Shijia0366/Environmental_Sensor_Group6/Environmental_Sensor_Group6/Enclosure/Right-Angle Female connector.SLDPRT

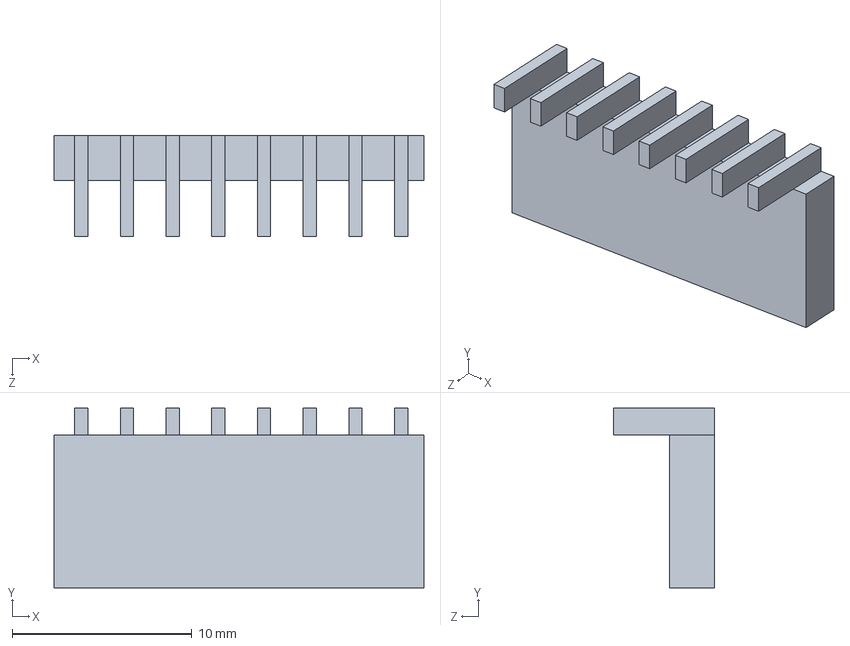
[picture p11: CAD file, 2025-12-15]
Environmental_Sensor_Group6/Enclosure/Right-Angle Female connector.SLDPRT
20.6 x 10.0 x 5.60 mm
