Shijia0366/Environmental_Sensor_Group6/Environmental_Sensor_Group6/Enclosure/button fitting component.SLDPRT

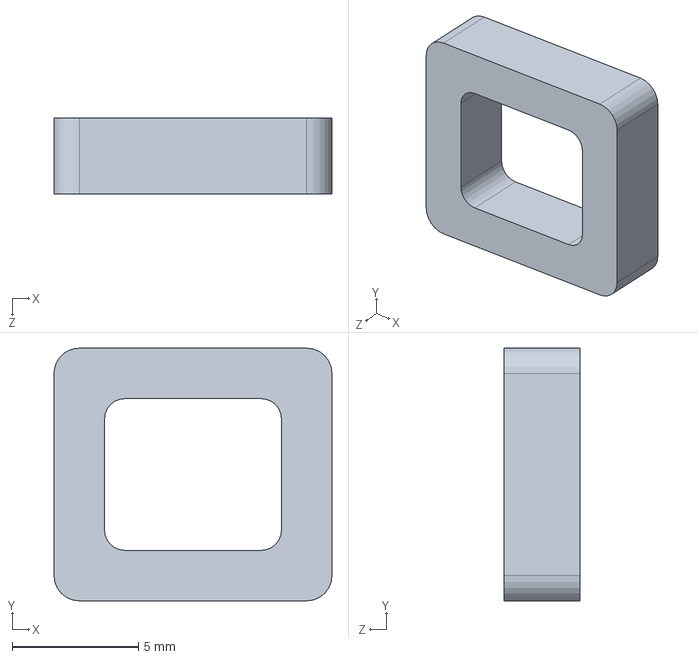
[picture p12: CAD file, 2025-12-15]
Environmental_Sensor_Group6/Enclosure/button fitting component.SLDPRT
11.0 x 10.0 x 3.00 mm
