Shijia0366/Environmental_Sensor_Group6/Environmental_Sensor_Group6/Enclosure/environmental pcb.step

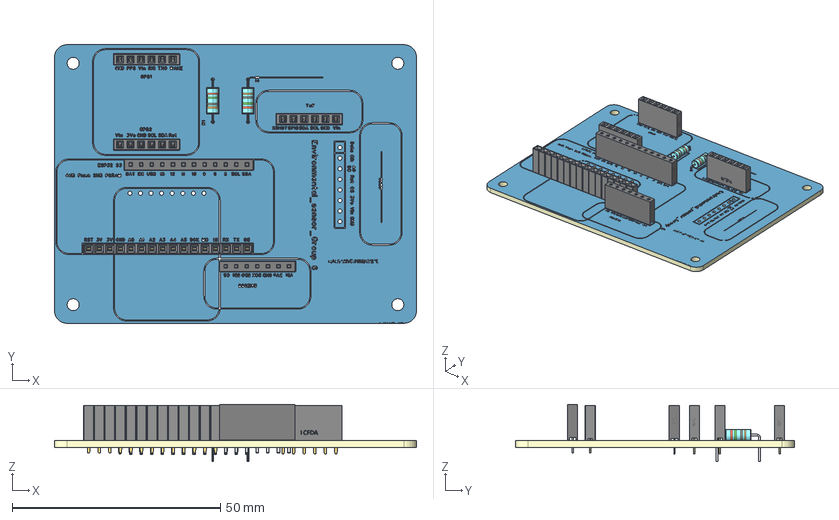
[picture p13: CAD file, 2025-12-15]
Environmental_Sensor_Group6/Enclosure/environmental pcb.step
87.0 x 67.0 x 13.7 mm
Board~KTJj
TopCopper~KTJj
BottomCopper~KTJj
TopSilkscreen~KTJj
BottomSilkscreen~KTJj
TopFpcStiffener~KTJj
BottomFpcStiffener~KTJj
HDR-TH_7P-P2.54-V-F~HDR-TH_7P-P2.54-F-LI-1X7P~KTJj
HDR-TH_12P-P2.54-V-F~HDR-TH_12P-P2.54-F-LI-1X12P~KTJj
HDR-TH_6P-P2.54-V-F~HDR-TH_6P-P2.54-V-F~KTJj x 3
HDR-TH_16P-P2.54-V-F-1~HDR2.54-F-LI-1X16P~KTJj
RES-TH_BD2.7-L6.2-P10.20-D0.4~RES-TH_BD2.7-L6.2-P10.20-D0.4~KTJj x 2
