Shijia0366/Environmental_Sensor_Group6/Environmental_Sensor_Group6/Enclosure/Button.SLDPRT

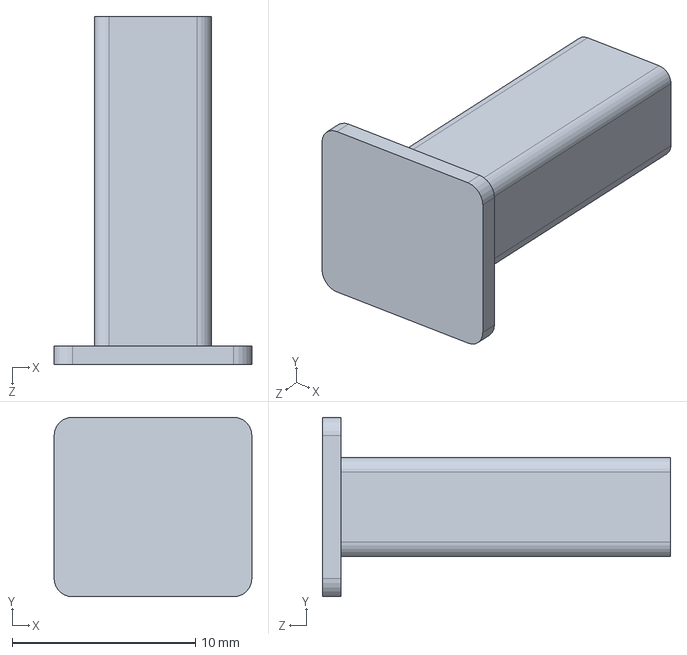
[picture p14: CAD file, 2025-12-15]
Environmental_Sensor_Group6/Enclosure/Button.SLDPRT
10.8 x 9.80 x 19.0 mm
