Shijia0366/Environmental_Sensor_Group6/Environmental_Sensor_Group6/Enclosure/oled.SLDPRT

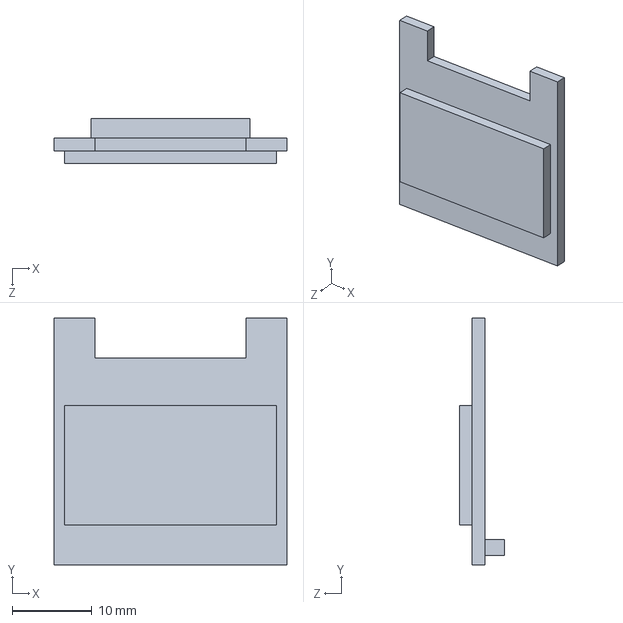
[picture p15: CAD file, 2025-12-15]
Environmental_Sensor_Group6/Enclosure/oled.SLDPRT
29.2 x 31.0 x 5.70 mm
