Shijia0366/Environmental_Sensor_Group6/Environmental_Sensor_Group6/Enclosure/Enclosure design 3D Group 6 - button-1.STL

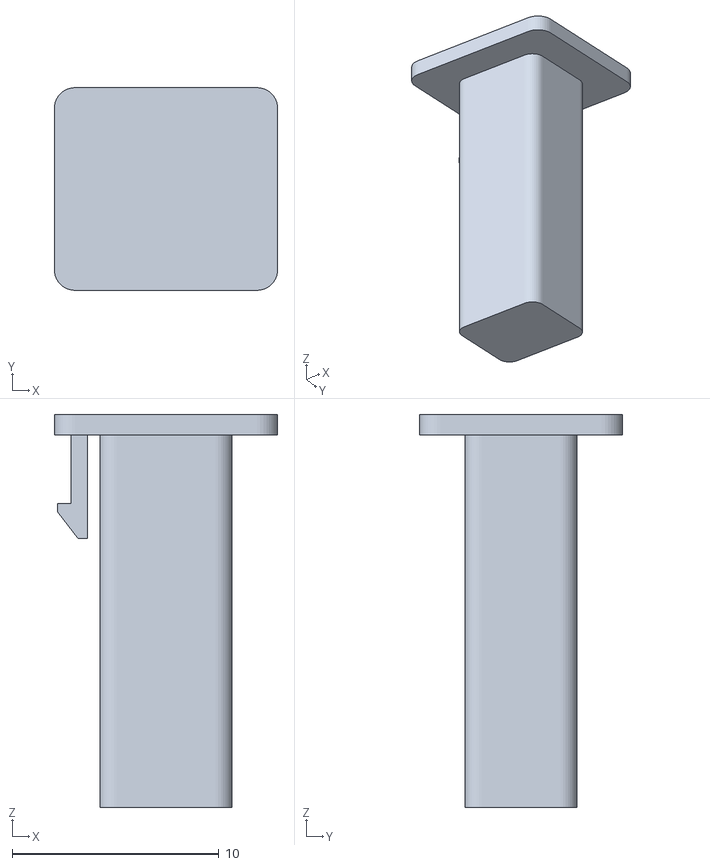
[picture p16: CAD file, 2025-12-15]
Environmental_Sensor_Group6/Enclosure/Enclosure design 3D Group 6 - button-1.STL
10.8 x 9.80 x 19.0
