Shijia0366/Environmental_Sensor_Group6/Environmental_Sensor_Group6/Enclosure/esp32.SLDPRT

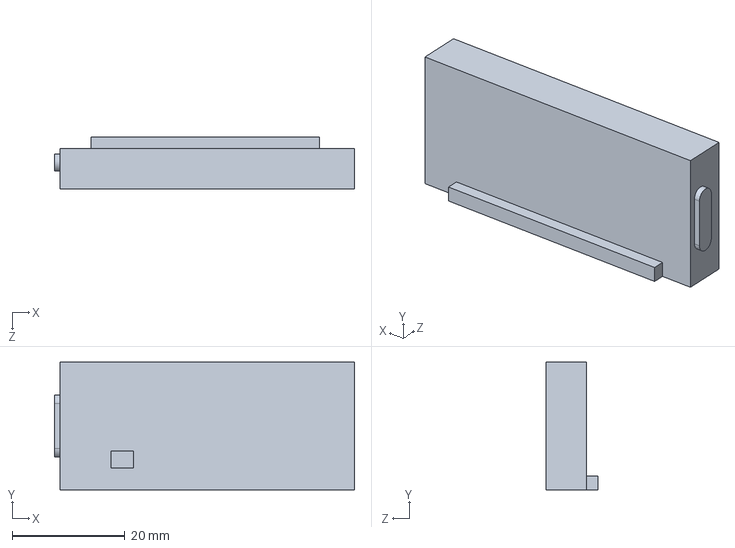
[picture p17: CAD file, 2025-12-15]
Environmental_Sensor_Group6/Enclosure/esp32.SLDPRT
53.3 x 22.7 x 9.20 mm
