Shijia0366/Environmental_Sensor_Group6/Environmental_Sensor_Group6/Data/Dec06_2000_2120_Indoor_Temp22.9C_Calibrated.csv

timestamp_ms | temp_c | hum_pct | press_hpa | gas_ohm | AQI | dist_mm | speed | lat | lon | alt_m | fix | acc_x | acc_y | acc_z | ppg_red | ppg_ir
5051 | 21.9 | 70.9 | 1000.5 | 7916 | 10 | 576 | nan | nan | nan | nan | 0 | nan | nan | nan | 0 | 0
10054 | 21.81 | 69.6 | 1000.5 | 16806 | 8 | 18 | nan | nan | nan | nan | 0 | nan | nan | nan | 0 | 0
15028 | 21.91 | 68.0 | 1000.5 | 24990 | 7 | 383 | nan | nan | nan | nan | 0 | nan | nan | nan | 0 | 0
20006 | 22.01 | 66.7 | 1000.5 | 29725 | 6 | 460 | nan | nan | nan | nan | 0 | nan | nan | nan | 0 | 0
24997 | 22.05 | 65.9 | 1000.5 | 36209 | 5 | 47 | nan | nan | nan | nan | 0 | nan | nan | nan | 0 | 0
29990 | 22.07 | 64.5 | 1000.5 | 41898 | 4 | 258 | nan | nan | nan | nan | 0 | nan | nan | nan | 0 | 0
34991 | 22.1 | 63.3 | 1000.5 | 45911 | 4 | 253 | nan | nan | nan | nan | 0 | nan | nan | nan | 0 | 0
39991 | 22.11 | 62.5 | 1000.5 | 50363 | 4 | 343 | nan | nan | nan | nan | 0 | nan | nan | nan | 0 | 0
44992 | 22.13 | 61.7 | 1000.5 | 53758 | 3 | 324 | nan | nan | nan | nan | 0 | nan | nan | nan | 0 | 0
49994 | 22.14 | 61.2 | 1000.5 | 56017 | 3 | 323 | nan | nan | nan | nan | 0 | nan | nan | nan | 0 | 0
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
