Shijia0366/Environmental_Sensor_Group6/Environmental_Sensor_Group6/Data/Dec07_0900_0950_Ark_Burlington_Danes_Calibrated.csv

timestamp_ms | temp_c | hum_pct | press_hpa | gas_ohm | AQI | dist_mm | speed | lat | lon | alt_m | fix | acc_x | acc_y | acc_z | ppg_red | ppg_ir
5047 | 15.07 | 64.4 | 999.3 | 5684 | 10 | 8 | nan | nan | nan | nan | 0 | nan | nan | nan | 0 | 0
10044 | 14.78 | 63.4 | 999.3 | 7761 | 10 | 13 | nan | nan | nan | nan | 0 | nan | nan | nan | 0 | 0
15021 | 14.72 | 62.7 | 999.3 | 13061 | 9 | 66 | nan | nan | nan | nan | 0 | nan | nan | nan | 0 | 0
20001 | 14.67 | 62.3 | 999.3 | 17567 | 8 | 23 | nan | nan | nan | nan | 0 | nan | nan | nan | 0 | 0
24998 | 14.23 | 62.5 | 999.3 | 21368 | 7 | 14 | nan | nan | nan | nan | 0 | nan | nan | nan | 0 | 0
29991 | 14.07 | 62.5 | 999.3 | 25286 | 7 | 17 | nan | nan | nan | nan | 0 | nan | nan | nan | 0 | 0
34993 | 14.18 | 62.6 | 999.3 | 28419 | 6 | 25 | nan | nan | nan | nan | 0 | nan | nan | nan | 0 | 0
39997 | 13.91 | 62.7 | 999.3 | 31204 | 6 | 13 | nan | nan | nan | nan | 0 | nan | nan | nan | 0 | 0
44995 | 13.57 | 62.7 | 999.3 | 34042 | 5 | 20 | nan | nan | nan | nan | 0 | nan | nan | nan | 0 | 0
49995 | 13.59 | 62.8 | 999.3 | 36802 | 5 | 13 | nan | nan | nan | nan | 0 | nan | nan | nan | 0 | 0
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
