Shijia0366/Environmental_Sensor_Group6/Environmental_Sensor_Group6/Data/Dec11_1210-1245_88WoodLane_Calibrated.csv

timestamp_ms | temp_c | hum_pct | press_hpa | gas_ohm | AQI | dist_mm | speed | lat | lon | alt_m | fix | acc_x | acc_y | acc_z | ppg_red | ppg_ir
9975 | 13.96 | 72.6 | 1020.1 | 6385 | 10 | 1 | 0.0 | nan | nan | nan | 0 | nan | nan | nan | 0 | 0
19971 | 13.32 | 71.7 | 1020.1 | 13672 | 9 | 27 | 0.0 | nan | nan | nan | 0 | nan | nan | nan | 0 | 0
29985 | 13.02 | 71.4 | 1020.1 | 20311 | 8 | 83 | 0.0 | nan | nan | nan | 0 | nan | nan | nan | 0 | 0
40003 | 12.8 | 71.3 | 1020.1 | 26711 | 6 | 10 | 0.0 | nan | nan | nan | 0 | nan | nan | nan | 0 | 0
49993 | 12.1 | 71.1 | 1020.1 | 31952 | 6 | 14 | 0.0 | nan | nan | nan | 0 | nan | nan | nan | 0 | 0
60016 | 11.8 | 70.9 | 1020.1 | 37220 | 5 | 27 | 0.0 | nan | nan | nan | 0 | nan | nan | nan | 0 | 0
70085 | 11.9 | 70.8 | 1020.1 | 42695 | 4 | 155 | 0.0 | nan | nan | nan | 0 | nan | nan | nan | 0 | 0
80057 | 11.5 | 70.8 | 1020.1 | 46817 | 4 | 68 | 0.0 | nan | nan | nan | 0 | nan | nan | nan | 0 | 0
90048 | 11.05 | 71.0 | 1020.0 | 51581 | 4 | 39 | 2.7 | 51.5125732 | -0.2254149 | 89.5 | 1 | nan | nan | nan | 0 | 0
100015 | 11.08 | 70.7 | 1020.0 | 56128 | 3 | 19 | 3.7 | 51.5126877 | -0.2253882 | 71.4 | 1 | nan | nan | nan | 0 | 0
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
