Shijia0366/Environmental_Sensor_Group6/Environmental_Sensor_Group6/Data/Dec11_1500_1530_RBKCCromwellRoad_Calibrated.csv

timestamp_ms | temp_c | hum_pct | press_hpa | gas_ohm | AQI | dist_mm | speed | lat | lon | alt_m | fix | acc_x | acc_y | acc_z | ppg_red | ppg_ir
10045.0 | 16.56 | 55.8 | 1013.5 | 35468.0 | 5.0 | 72.0 | 0.0 | nan | nan | nan | 0.0 | nan | nan | nan | 0.0 | 0.0
20030.0 | 16.22 | 55.9 | 1013.4 | 38762.0 | 5.0 | 58.0 | 0.0 | nan | nan | nan | 0.0 | nan | nan | nan | 0.0 | 0.0
30047.0 | 16.13 | 56.2 | 1013.5 | 82469.0 | 2.0 | 99.0 | 0.0 | nan | nan | nan | 0.0 | nan | nan | nan | 0.0 | 0.0
40038.0 | 16.16 | 56.3 | 1013.5 | 136521.0 | 1.0 | 80.0 | 0.0 | nan | nan | nan | 0.0 | nan | nan | nan | 0.0 | 0.0
50029.0 | 15.93 | 56.4 | 1013.6 | 81548.0 | 2.0 | 24.0 | 0.0 | nan | nan | nan | 0.0 | nan | nan | nan | 0.0 | 0.0
60059.0 | 15.92 | 56.4 | 1013.6 | 79991.0 | 2.0 | 85.0 | 0.0 | nan | nan | nan | 0.0 | nan | nan | nan | 0.0 | 0.0
69991.0 | 15.65 | 56.2 | 1013.4 | 82341.0 | 2.0 | 44.0 | 0.0 | nan | nan | nan | 0.0 | nan | nan | nan | 0.0 | 0.0
80057.0 | 15.72 | 56.3 | 1013.5 | 125021.0 | 1.0 | 48.0 | 0.0 | nan | nan | nan | 0.0 | nan | nan | nan | 0.0 | 0.0
89981.0 | 15.19 | 55.8 | 1013.5 | 128001.0 | 1.0 | 89.0 | 0.0 | nan | nan | nan | 0.0 | nan | nan | nan | 0.0 | 0.0
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
