Shijia0366/Environmental_Sensor_Group6/Environmental_Sensor_Group6/Code/Autonomous_Nodes_Environmental_Sensors/src/hal/Buses.h

#pragma once
#include <Arduino.h>
#include <Wire.h>
#include <SPI.h>

// HAL: Hardware Abstraction Layer for shared buses
namespace HAL {
  // I2C / SPI singletons (references to global instances)
  TwoWire& getWire();      // default I2C (Wire)
  SPIClass& getSPI();      // default SPI (SPI)

  // Init functions (use timings defined in config.h)
  bool beginI2C();         // powers I2C domain, waits, begin Wire, setClock
  bool beginSPI();         // begin SPI, optionally with custom pins in Buses.cpp

}
